7west/PicoTop/SOFTWARE/src/shellwork/includes.h

#include <stdio.h>
#include <string.h>

#include "pico/stdlib.h"
#include "hardware/gpio.h"
#include "pico/multicore.h"
#include "pico/sem.h"

#include "terminal.h"
#include "os_debug.h"
#include "usb_kbd.h"
#include "rtc.h"
#include "prog.h"
#include "shell.h"
#include "vfs.h"
#include "batt.h"
#include "buzz.h"
#include "vault.h"
#include "video_out.h"

#include "bsp/board.h"
#include "tusb.h"
#include "tusb_config.h"
